Aravind-Sundararajan/sunnycnc/stls_and_scad/bearing.scad

/*
	This is a spacer for testing purposes in fine-tuning the x-axis gantry.
*/
difference(){
cylinder(7.5,d=8,center=true,$fn=360);
cylinder(9,d=5,center=true,$fn=360);
}
