Aravind-Sundararajan/sunnycnc/stls_and_scad/washer.scad

/*
	This is just a simple spacer for 5mm bolts
*/
difference(){
cylinder(3,6,6,true);
cylinder(4,3.5,3.5,true);
}
